JFUcayal/Bat-mon-v1/firmware_v1.0/Core/Src/usart.c

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
/* Includes ------------------------------------------------------------------*/
#include "usart.h"

UART_HandleTypeDef hlpuart1;

/* LPUART1 init function */

void MX_LPUART1_UART_Init(void)
{

  hlpuart1.Instance = LPUART1;
  hlpuart1.Init.BaudRate = 115200;
  hlpuart1.Init.WordLength = UART_WORDLENGTH_8B;
  hlpuart1.Init.StopBits = UART_STOPBITS_1;
  hlpuart1.Init.Parity = UART_PARITY_NONE;
  hlpuart1.Init.Mode = UART_MODE_TX_RX;
  hlpuart1.Init.HwFlowCtl = UART_HWCONTROL_NONE;
  hlpuart1.Init.OneBitSampling = UART_ONE_BIT_SAMPLE_DISABLE;
  hlpuart1.AdvancedInit.AdvFeatureInit = UART_ADVFEATURE_NO_INIT;
  if (HAL_UART_Init(&hlpuart1) != HAL_OK)
  {
    Error_Handler();
  }
}

void HAL_UART_MspInit(UART_HandleTypeDef* uartHandle)
{

  GPIO_InitTypeDef GPIO_InitStruct = {0};
  if(uartHandle->Instance==LPUART1)
  {
    /* LPUART1 clock enable */
    __HAL_RCC_LPUART1_CLK_ENABLE();

    __HAL_RCC_GPIOB_CLK_ENABLE();
    /**LPUART1 GPIO Configuration
    PB10     ------> LPUART1_TX
    PB11     ------> LPUART1_RX
    */
    GPIO_InitStruct.Pin = GPIO_PIN_10|GPIO_PIN_11;
    GPIO_InitStruct.Mode = GPIO_MODE_AF_PP;
    GPIO_InitStruct.Pull = GPIO_NOPULL;
    GPIO_InitStruct.Speed = GPIO_SPEED_FREQ_VERY_HIGH;
    GPIO_InitStruct.Alternate = GPIO_AF6_LPUART1;
    HAL_GPIO_Init(GPIOB, &GPIO_InitStruct);

  }
}

void HAL_UART_MspDeInit(UART_HandleTypeDef* uartHandle)
{

  if(uartHandle->Instance==LPUART1)
  {
    /* Peripheral clock disable */
    __HAL_RCC_LPUART1_CLK_DISABLE();

    /**LPUART1 GPIO Configuration
    PB10     ------> LPUART1_TX
    PB11     ------> LPUART1_RX
    */
    HAL_GPIO_DeInit(GPIOB, GPIO_PIN_10|GPIO_PIN_11);

  }
}
